ashiqrahmana/Intelligent-Line-Marking-Bot/Code/ground.jpg

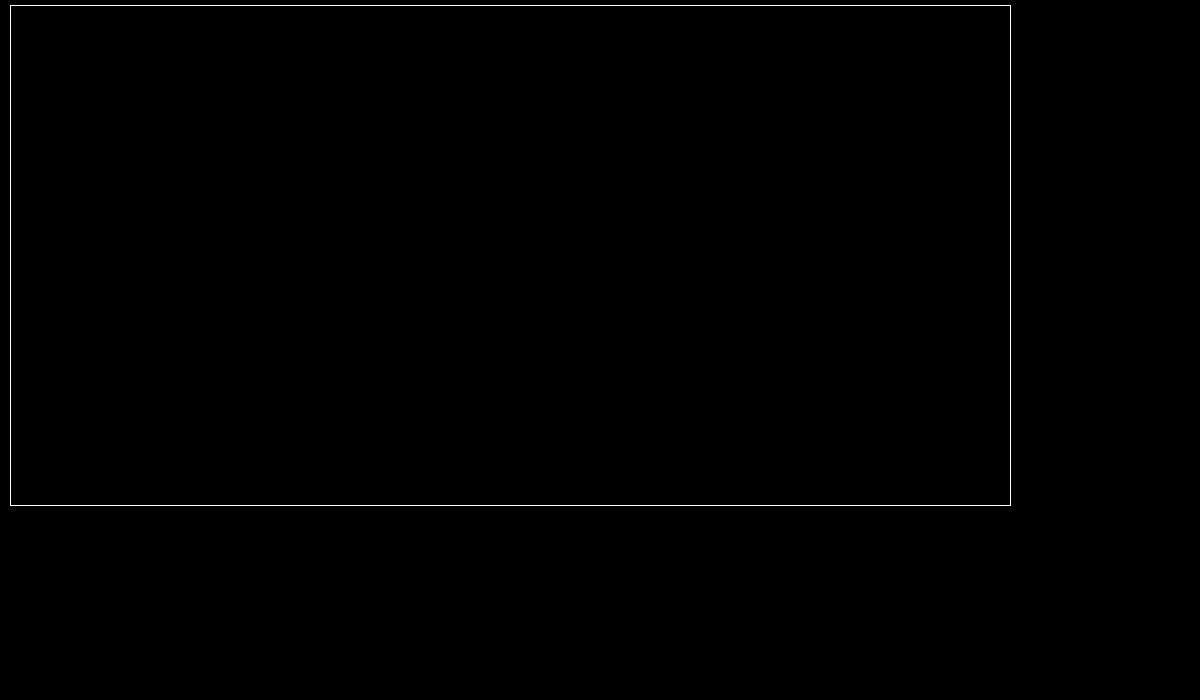
Code/ground.jpg
