ashiqrahmana/Intelligent-Line-Marking-Bot/Documentation/Media/IMG_6448.JPG

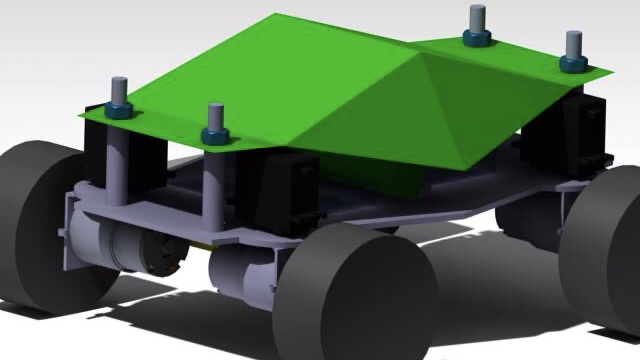
Documentation/Media/IMG_6448.JPG
