ashiqrahmana/Intelligent-Line-Marking-Bot/Documentation/Team/Vallarasu.jpeg

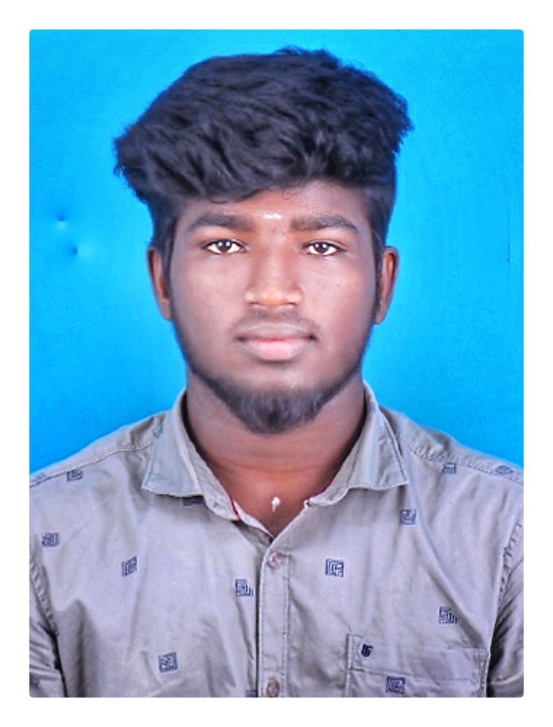
Documentation/Team/Vallarasu.jpeg
