ashiqrahmana/Intelligent-Line-Marking-Bot/Documentation/Team/Veni.jpeg

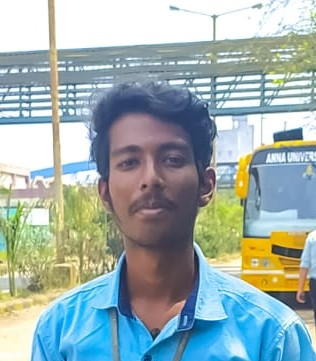
Documentation/Team/Veni.jpeg
