ashiqrahmana/Intelligent-Line-Marking-Bot/Code/Code_LM_bot_1/main/Sensor_cal.ino

/*float ultra_dist() {
  // Clears the trigPin condition
  digitalWrite(trigPin, LOW);
  delayMicroseconds(2);
  // Sets the trigPin HIGH (ACTIVE) for 10 microseconds
  digitalWrite(trigPin, HIGH);
  delayMicroseconds(10);
  digitalWrite(trigPin, LOW);
  // Reads the echoPin, returns the sound wave travel time in microseconds
  duration = pulseIn(echoPin, HIGH);
  // Calculating the distance
  distance = duration * 0.034 / 2; // Speed of sound wave divided by 2 (go and back)
  // Displays the distance on the Serial Monitor
  //Serial.print("Distance: ");
  //Serial.print(distance);
  //Serial.println(" cm");
  return distance;
}*/
