ashiqrahmana/Intelligent-Line-Marking-Bot/Code/Code_LM_bot_1/main/motor_control.ino

void stop_motor(){

  digitalWrite(IN1[0],LOW);
  digitalWrite(IN2[0],LOW);
  
  digitalWrite(IN1[1],LOW);
  digitalWrite(IN2[1],LOW);
  
  digitalWrite(IN1[2],LOW);
  digitalWrite(IN2[2],LOW);
  
  digitalWrite(IN1[3],LOW);
  digitalWrite(IN2[3],LOW);
    
}
