ashiqrahmana/Intelligent-Line-Marking-Bot/Code/Code_LM_bot/Code_LM_bot.ino

  //--------------------------------------------------------------------------------------
//parameters for calculation
//--------------------------------------------------------------------------------------
const float WheelDist = 0.5; //wheel base in meters
float phi;
const float wheelRadius = 0.05;
float curr_pos[] = {0,0,0};
float target_pos[] = {0,0,0};
float Earth_Radius = 6371000;

void setup() {
  // put your setup code here, to run once:
  initMPU();
  initGPS();
}

void loop() {
  // put your main code here, to run repeatedly:

}
